tobychui/PD-Adjustable-DC-Power-Supply/3D model/v3/bottom.stl

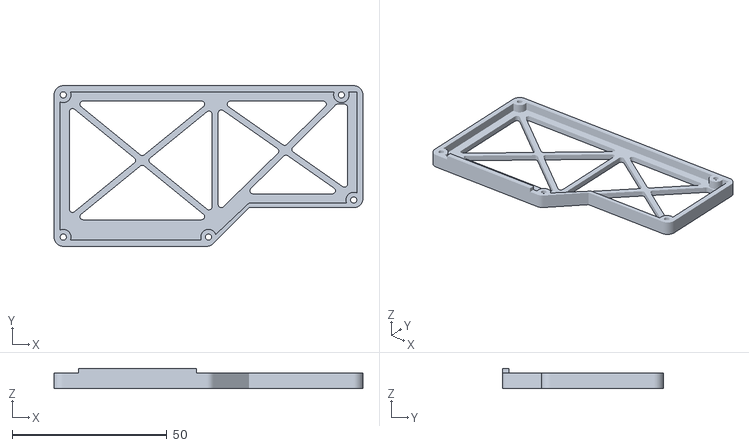
[picture p27: CAD file, 2025-02-16, an earlier design]
3D model/v3/bottom.stl
100.0 x 52.0 x 6.50
