tobychui/PD-Adjustable-DC-Power-Supply/firmware/pd-psu_v3/display_char.h

#ifndef DISPLAY_CHAR_H
#define DISPLAY_CHAR_H
#define display16X16_number { \
    display16X16_0, \
    display16X16_1, \
    display16X16_2, \
    display16X16_3, \
    display16X16_4, \
    display16X16_5, \
    display16X16_6, \
    display16X16_7, \
    display16X16_8, \
    display16X16_9  \
}
#define display16X16_0  { \
    0b0000000000000000, \
    0b0000011111100000, \
    0b0000111111110000, \
    0b0001100000011000, \
    0b0011000000001100, \
    0b0011000000001100, \
    0b0110000000000110, \
    0b0110000000000110, \
    0b0110000000000110, \
    0b0110000000000110, \
    0b0011000000001100, \
    0b0011000000001100, \
    0b0001100000011000, \
    0b0000111111110000, \
    0b0000011111100000, \
    0b0000000000000000  \
}
#define display16X16_1  { \
    0b0000000000000000, \
    0b0000000111000000, \
    0b0000001111000000, \
    0b0000011111000000, \
    0b0000110111000000, \
    0b0001100111000000, \
    0b0000000111000000, \
    0b0000000111000000, \
    0b0000000111000000, \
    0b0000000111000000, \
    0b0000000111000000, \
    0b0000000111000000, \
    0b0000000111000000, \
    0b0011111111111100, \
    0b0011111111111100, \
    0b0000000000000000  \
}

#define display16X16_2  { \
    0b0000000000000000, \
    0b0000011111110000, \
    0b0000111111111000, \
    0b0001110000011100, \
    0b0011000000001100, \
    0b0011000000011100, \
    0b0000000000111000, \
    0b0000000001110000, \
    0b0000000011100000, \
    0b0000000111000000, \
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
    0b0011111000000000, \
    0b0111100000000000, \
    0b0110000000000000, \
    0b0111000000000000, \
    0b0111100000000000, \
    0b0011111000000000, \
    0b0000111111000000, \
    0b0000000111111000, \
    0b0000000001111110, \
    0b0000000000001110, \
    0b0000000000000000  \
}
#endif
